maximyudayev/TMD351-Rigid-Flex-HDMI-Switch/images/Eagle buildup.png

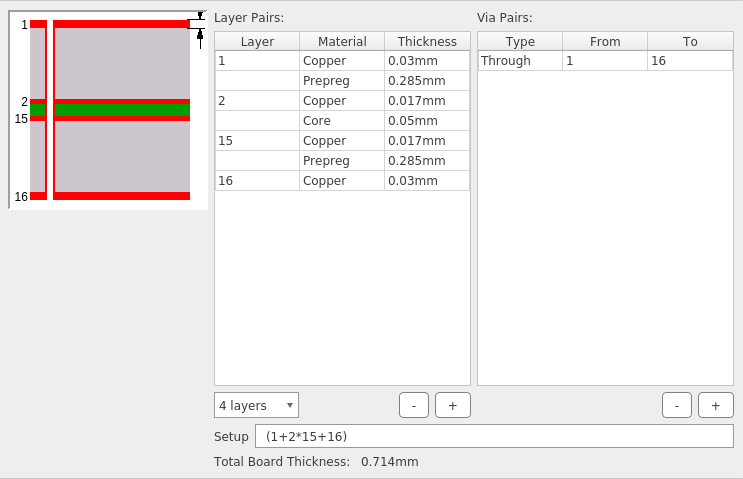
images/Eagle buildup.png
