maximyudayev/TMD351-Rigid-Flex-HDMI-Switch/images/WE Buildup 1Ri2F1Ri.png

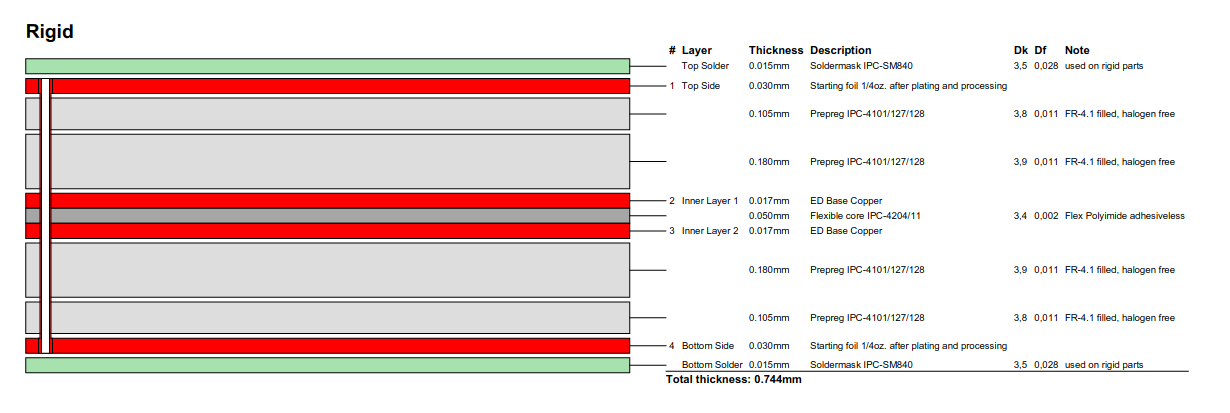
images/WE Buildup 1Ri2F1Ri.png
