maximyudayev/TMD351-Rigid-Flex-HDMI-Switch/images/Measures and mechanical layer unfilled.png

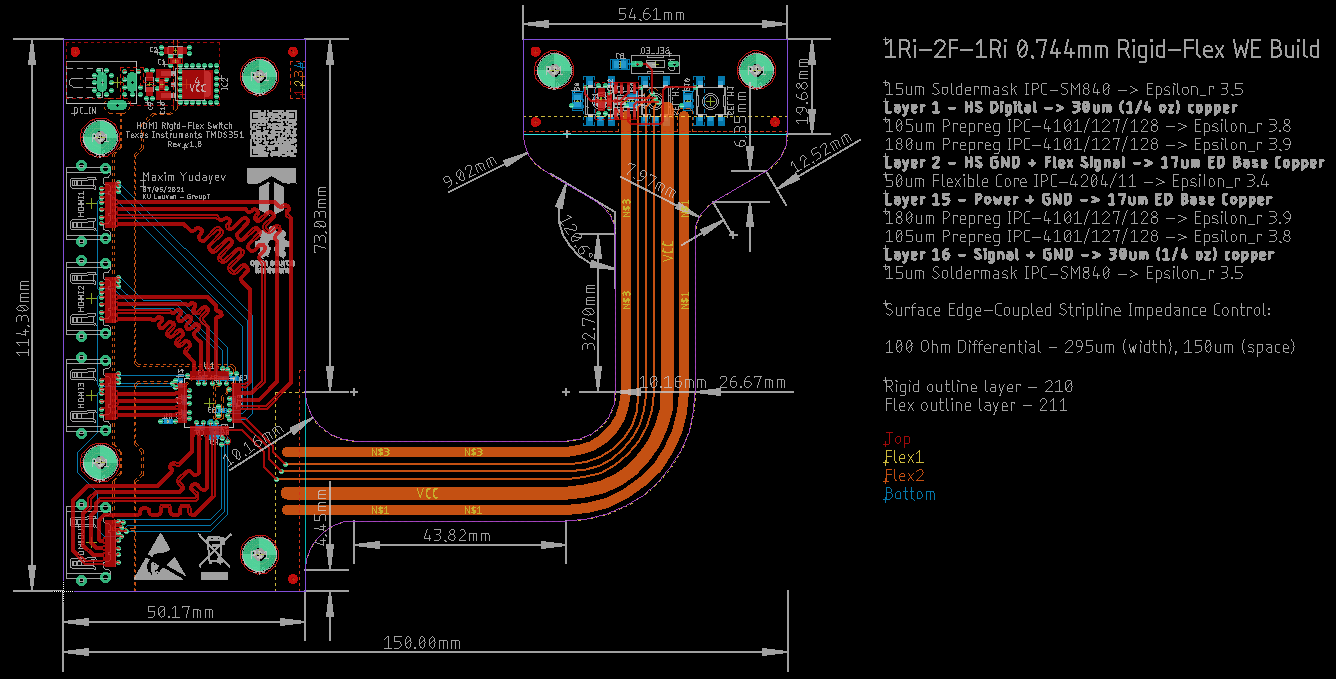
images/Measures and mechanical layer unfilled.png
